rushabhcodes/fidget-counter/previews/3d.png

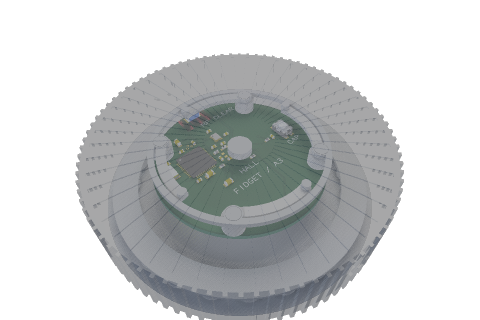
previews/3d.png
