rushabhcodes/fidget-counter/previews/pcb-bottom-top-coordinates.png

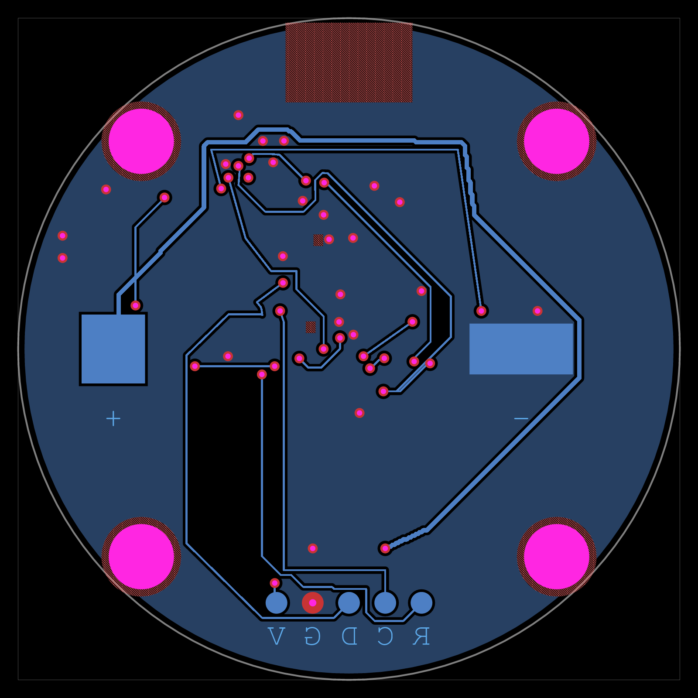
previews/pcb-bottom-top-coordinates.png
