rushabhcodes/fidget-counter/mechanical/Print_STL/Cap_Release_Key_Print_2.stl

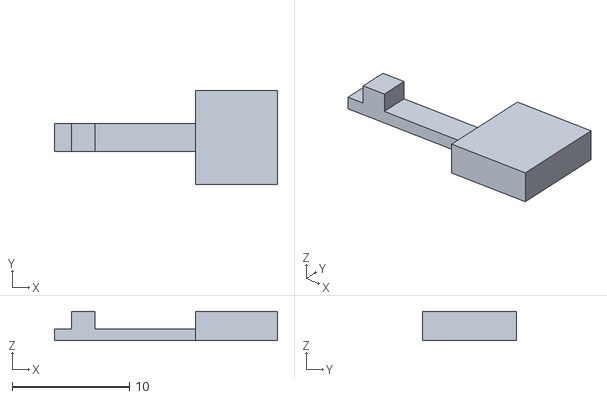
[picture p22: CAD file, 2026-10-08]
mechanical/Print_STL/Cap_Release_Key_Print_2.stl
19.0 x 8.00 x 2.50
