rushabhcodes/fidget-counter/mechanical/STEP_Parts/Stationary_Housing.step

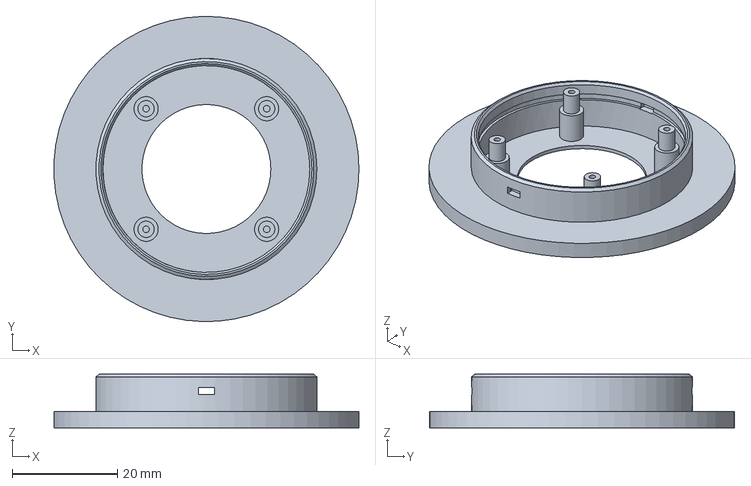
[picture p23: CAD file, 2026-10-08]
mechanical/STEP_Parts/Stationary_Housing.step
58.0 x 58.0 x 10.2 mm
