rushabhcodes/fidget-counter/mechanical/Print_STL/PCB_Spacer_Print_4.stl

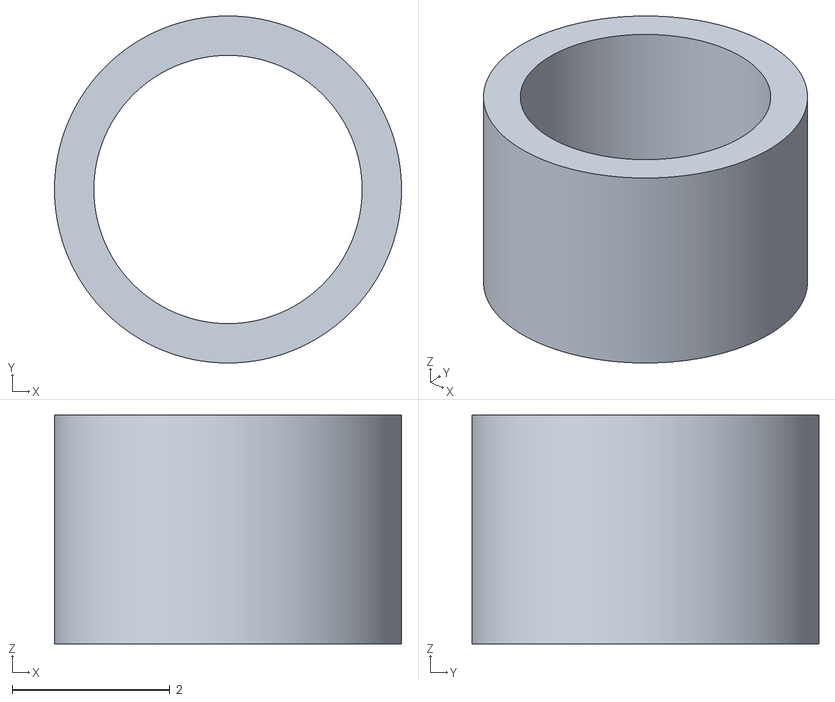
[picture p24: CAD file, 2026-10-08]
mechanical/Print_STL/PCB_Spacer_Print_4.stl
4.40 x 4.40 x 2.90
