rushabhcodes/fidget-counter/mechanical/Circuit_Models/Bottom_Cover.obj

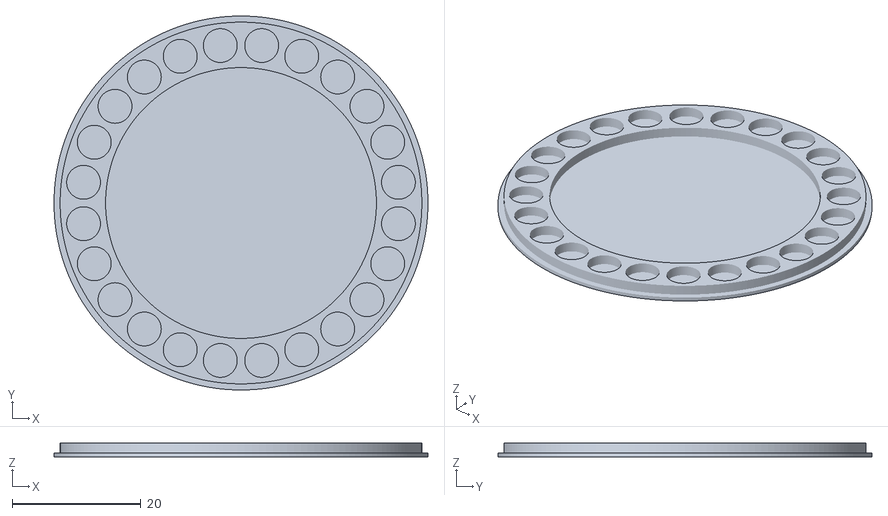
[picture p25: CAD file, 2026-10-08]
mechanical/Circuit_Models/Bottom_Cover.obj
58.0 x 58.0 x 2.15
