rushabhcodes/fidget-counter/mechanical/Circuit_Models/Phone_Pad.obj

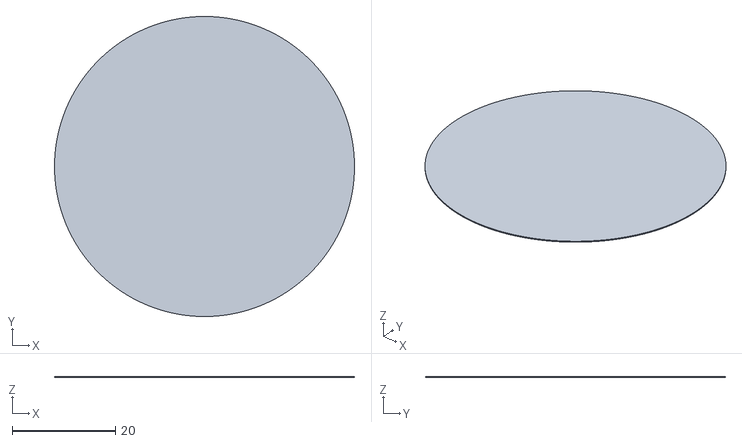
[picture p26: CAD file, 2026-10-08]
mechanical/Circuit_Models/Phone_Pad.obj
58.0 x 58.0 x 0.2
