rushabhcodes/fidget-counter/mechanical/Circuit_Models/Magnetic_Shield.obj

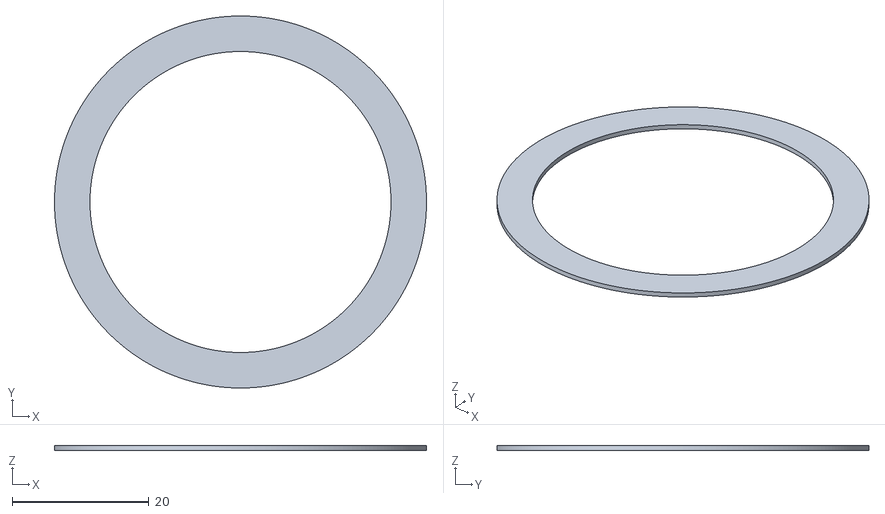
[picture p27: CAD file, 2026-10-08]
mechanical/Circuit_Models/Magnetic_Shield.obj
54.5 x 54.4 x 0.7
