rushabhcodes/fidget-counter/mechanical/STEP_Parts/PCB_Lift_Pick.step

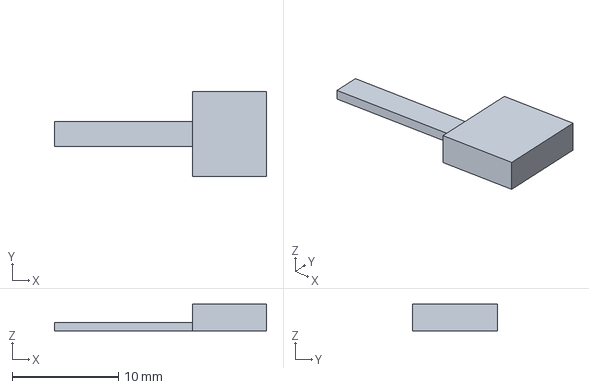
[picture p28: CAD file, 2026-10-08]
mechanical/STEP_Parts/PCB_Lift_Pick.step
20.0 x 8.00 x 2.50 mm
