rushabhcodes/fidget-counter/mechanical/Circuit_Models/MagSafe_Magnet_Array.obj

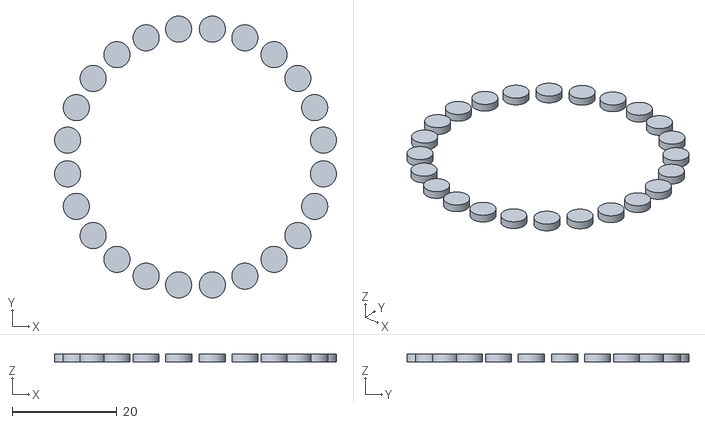
[picture p29: CAD file, 2026-10-08]
mechanical/Circuit_Models/MagSafe_Magnet_Array.obj
53.8 x 53.8 x 1.50
