rushabhcodes/fidget-counter/mechanical/STEP_Parts/PCB_Spacer_Bushings.step

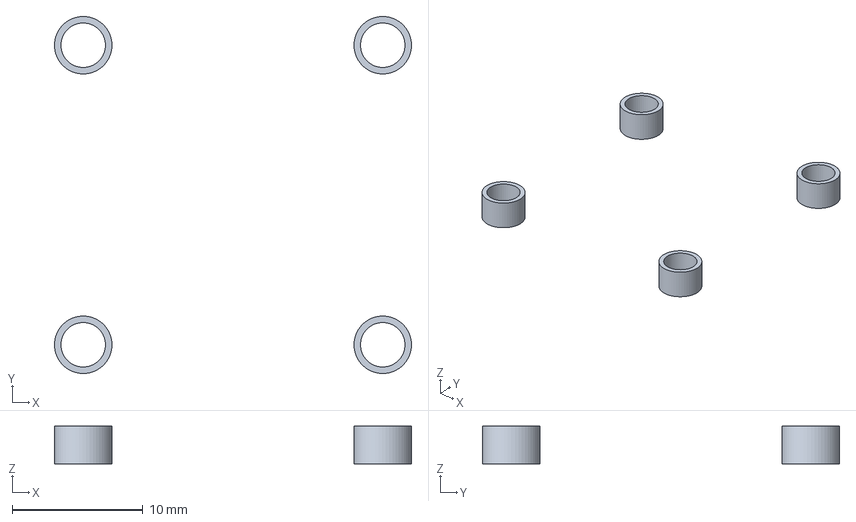
[picture p30: CAD file, 2026-10-08]
mechanical/STEP_Parts/PCB_Spacer_Bushings.step
27.3 x 27.3 x 2.90 mm
