rushabhcodes/fidget-counter/mechanical/Circuit_Models/Encoder_Shim.obj

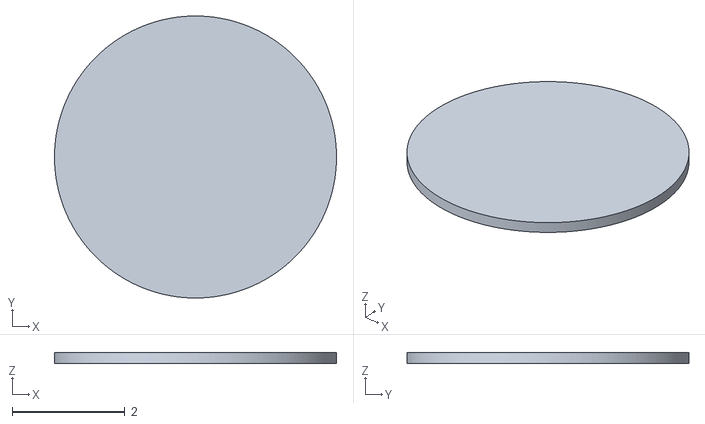
[picture p31: CAD file, 2026-10-07]
mechanical/Circuit_Models/Encoder_Shim.obj
5.00 x 5.00 x 0.2
