rushabhcodes/fidget-counter/mechanical/STEP_Parts/Flexure_Retention_System.step

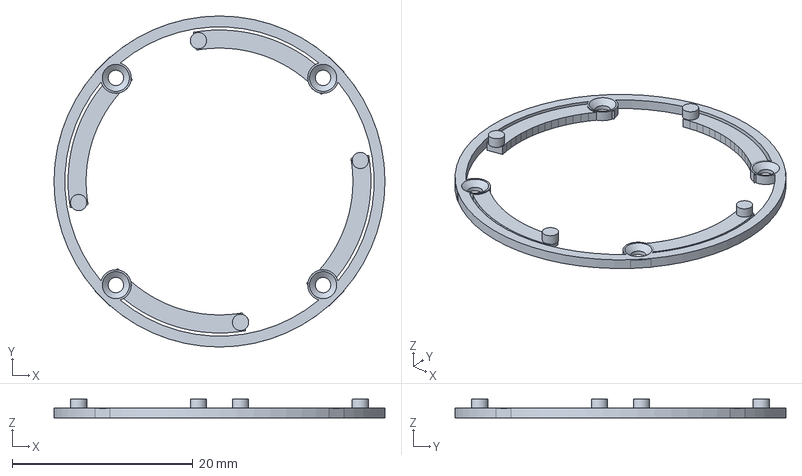
[picture p32: CAD file, 2026-10-07]
mechanical/STEP_Parts/Flexure_Retention_System.step
36.6 x 36.6 x 2.05 mm
