rushabhcodes/fidget-counter/mechanical/Circuit_Models/Flexure_Retention_System.obj

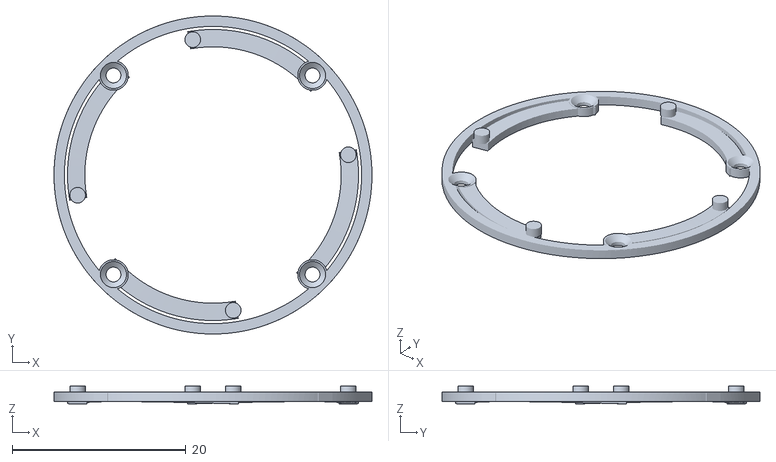
[picture p33: CAD file, 2026-10-07]
mechanical/Circuit_Models/Flexure_Retention_System.obj
36.6 x 36.6 x 2.06
