rushabhcodes/fidget-counter/mechanical/Circuit_Models/Flexure_Fasteners.obj

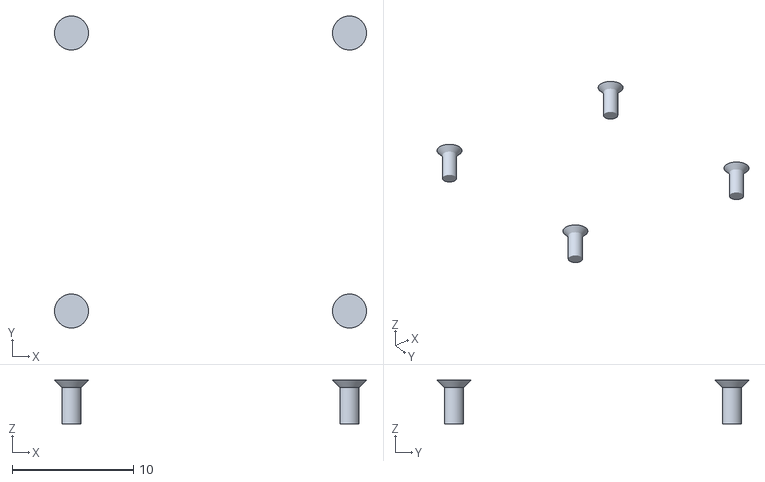
[picture p34: CAD file, 2026-10-07]
mechanical/Circuit_Models/Flexure_Fasteners.obj
25.7 x 25.7 x 3.60
