rushabhcodes/fidget-counter/mechanical/Circuit_Models/Encoder_Magnet.obj

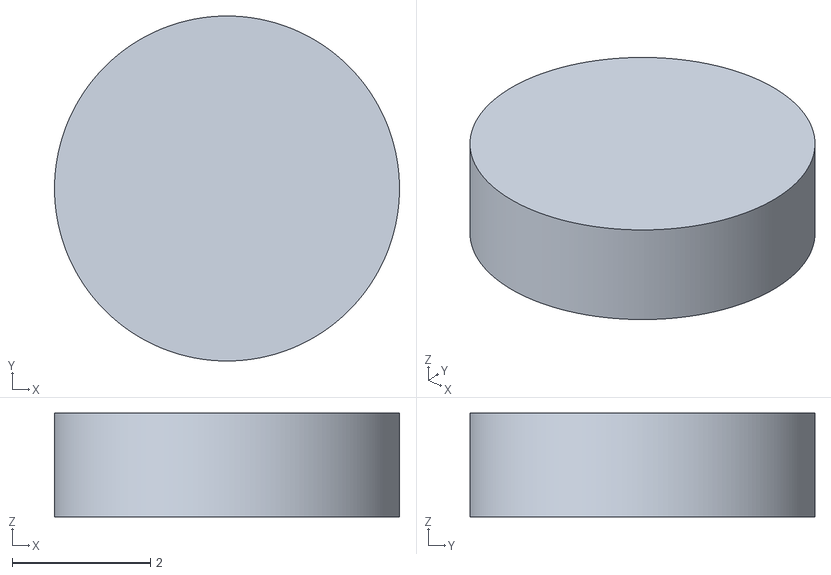
[picture p35: CAD file, 2026-10-07]
mechanical/Circuit_Models/Encoder_Magnet.obj
5.00 x 5.00 x 1.50
