rushabhcodes/fidget-counter/mechanical/Circuit_Models/CR2032.obj

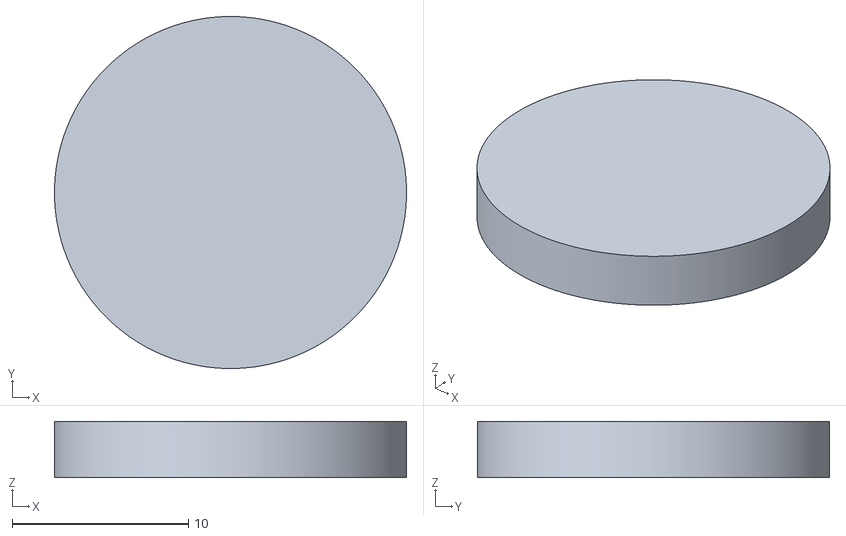
[picture p36: CAD file, 2026-10-07]
mechanical/Circuit_Models/CR2032.obj
20.0 x 20.0 x 3.20
