rushabhcodes/fidget-counter/previews/assembly-bottom.png

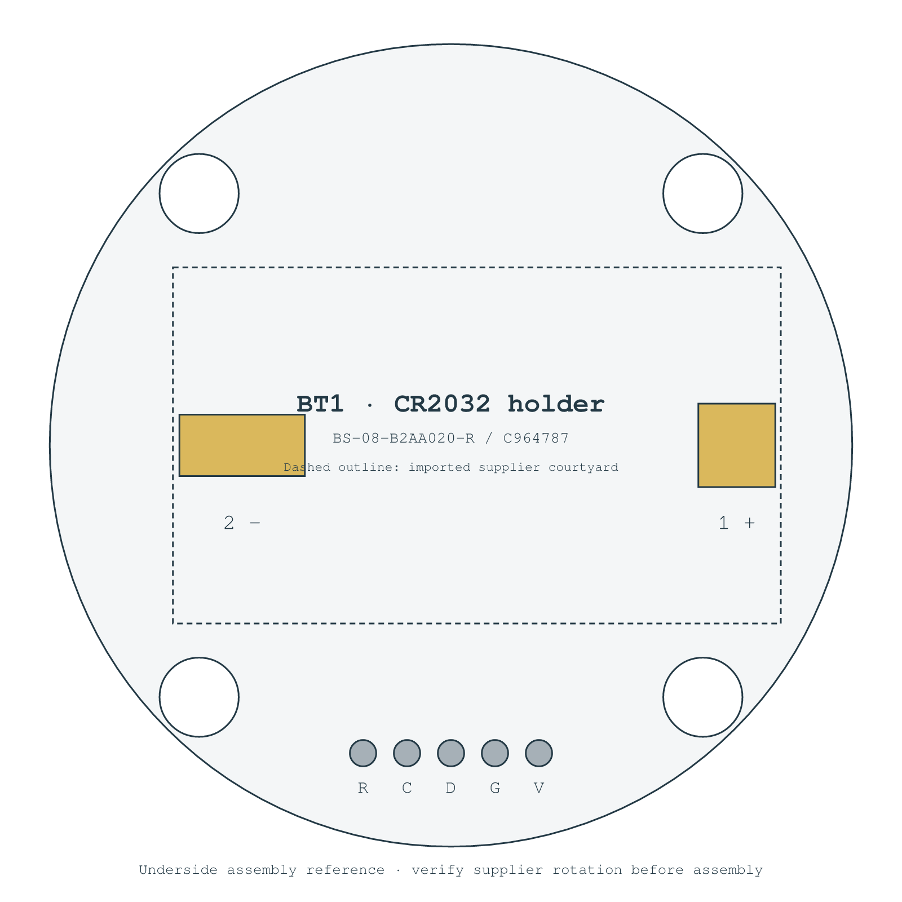
previews/assembly-bottom.png
