rushabhcodes/fidget-counter/previews/assembly-top.png

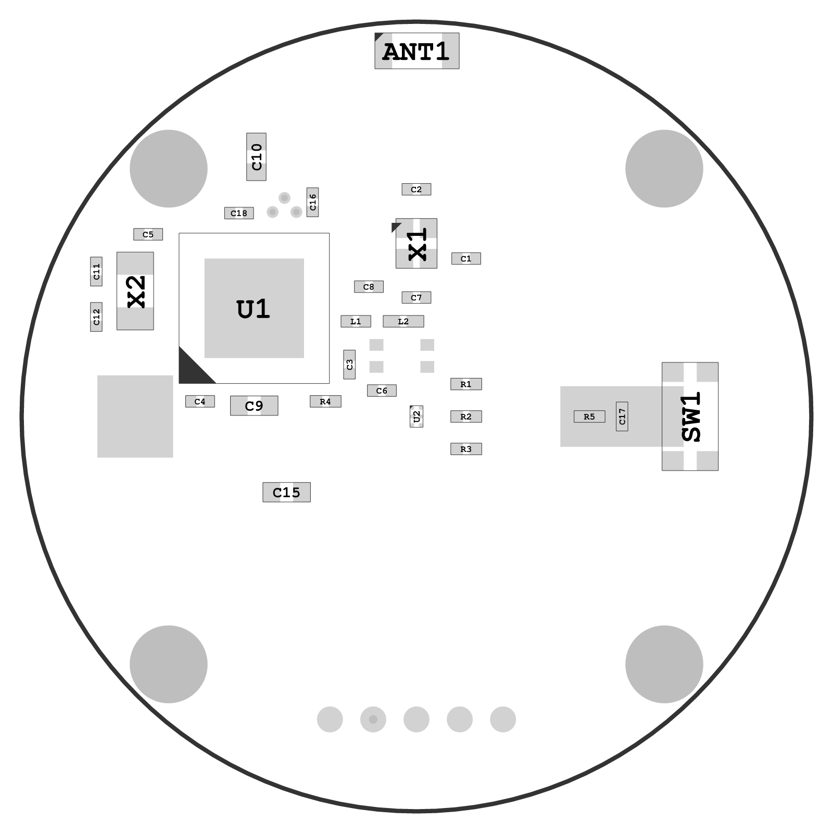
previews/assembly-top.png
