rushabhcodes/fidget-counter/previews/schematic-1-power-debug.png

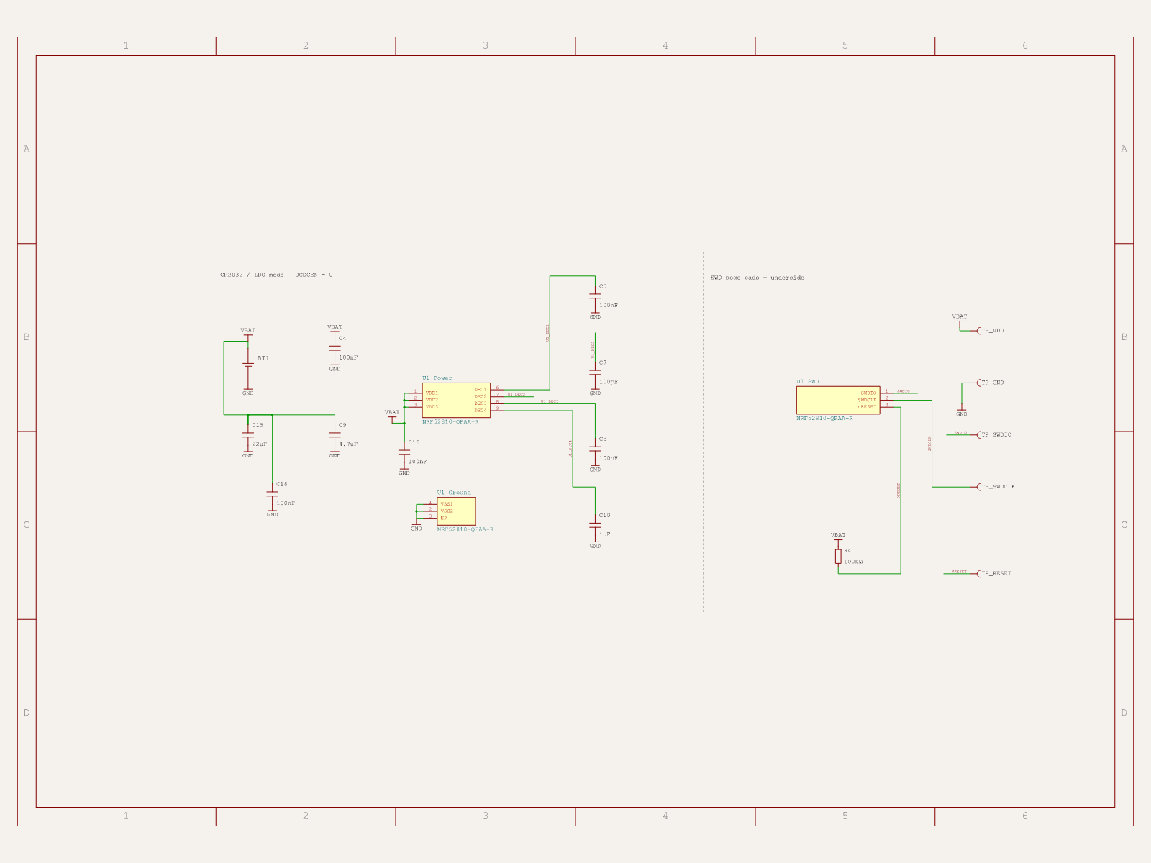
previews/schematic-1-power-debug.png
